Marc-Bender/UltraSonicWatertankLevelDisplay/Firmware/measure.h

/*
 * measure.h
 *
 * Created: 04.06.2024 22:21:46
 *  Author: marc
 */ 


#ifndef MEASURE_H_
#define MEASURE_H_

#include <stdint.h>
#include <stdbool.h>

uint16_t Meas_BatVoltage(void);

#endif /* MEASURE_H_ */
